BryanSmithDev/HeliosWatch/HeliosWatch_Documentation/Images/androidAppFilters.png

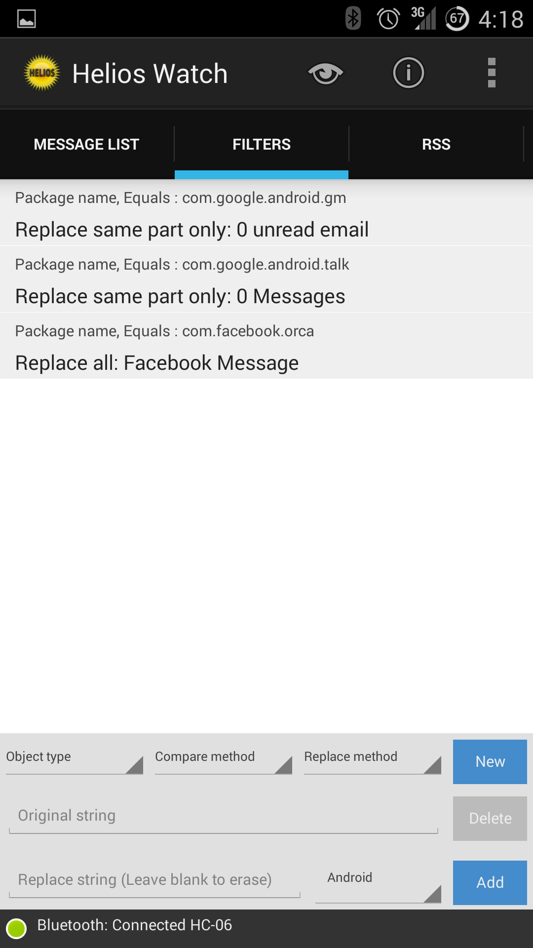
HeliosWatch_Documentation/Images/androidAppFilters.png
