BryanSmithDev/HeliosWatch/HeliosWatch_Documentation/Images/androidAppMessageList.png

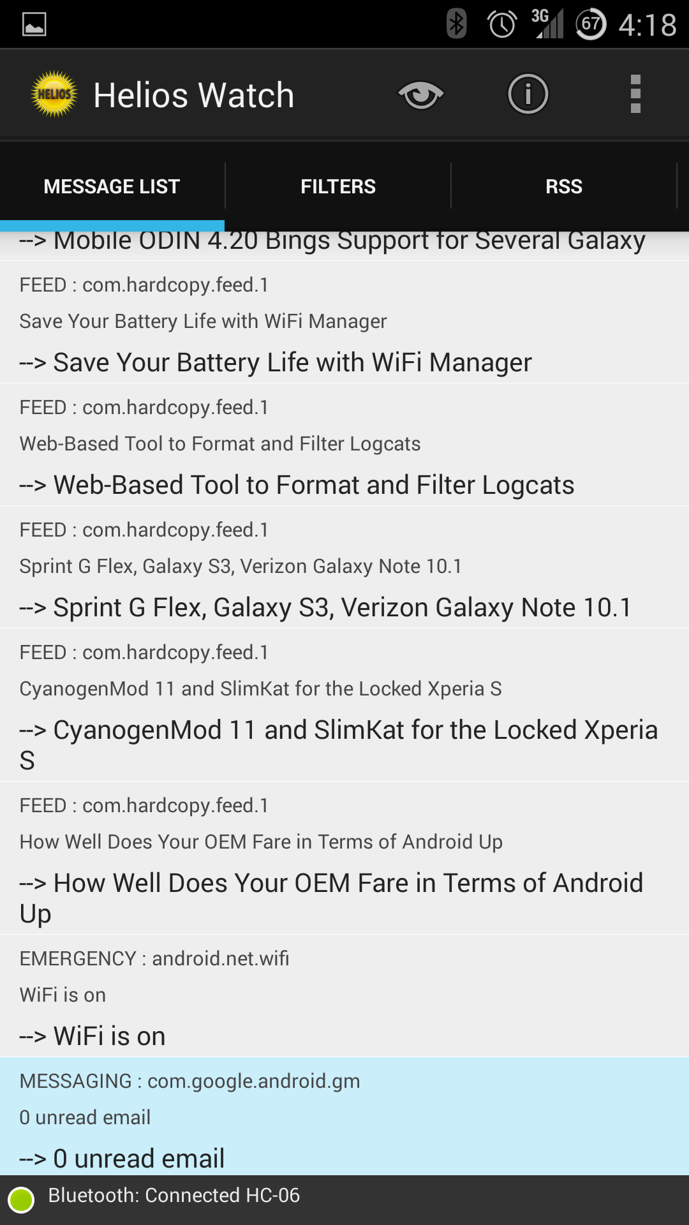
HeliosWatch_Documentation/Images/androidAppMessageList.png
