BryanSmithDev/HeliosWatch/HeliosWatch_Documentation/Images/androidAppRSS.png

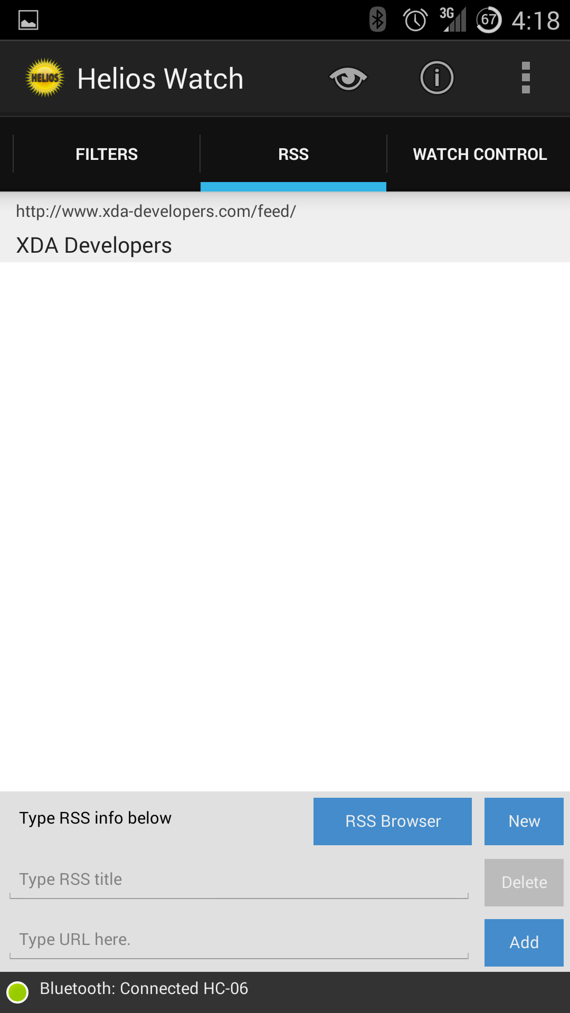
HeliosWatch_Documentation/Images/androidAppRSS.png
