BryanSmithDev/HeliosWatch/HeliosWatch_Documentation/Images/androidAppWatchControl.png

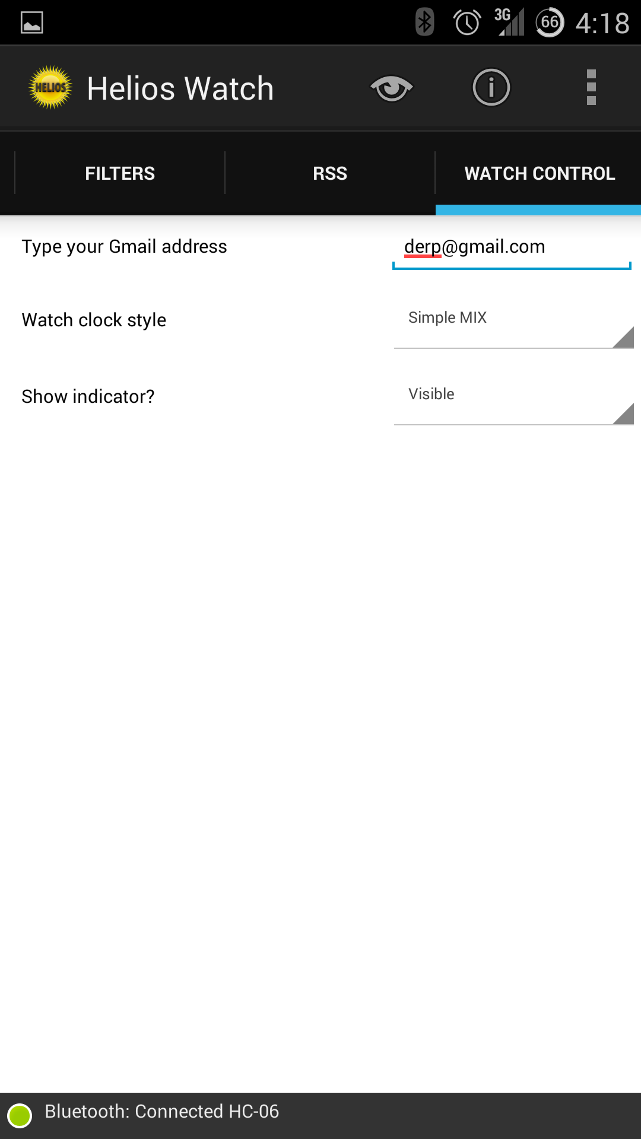
HeliosWatch_Documentation/Images/androidAppWatchControl.png
