BryanSmithDev/HeliosWatch/HeliosWatch_Documentation/Images/BatteryPrep1.jpg

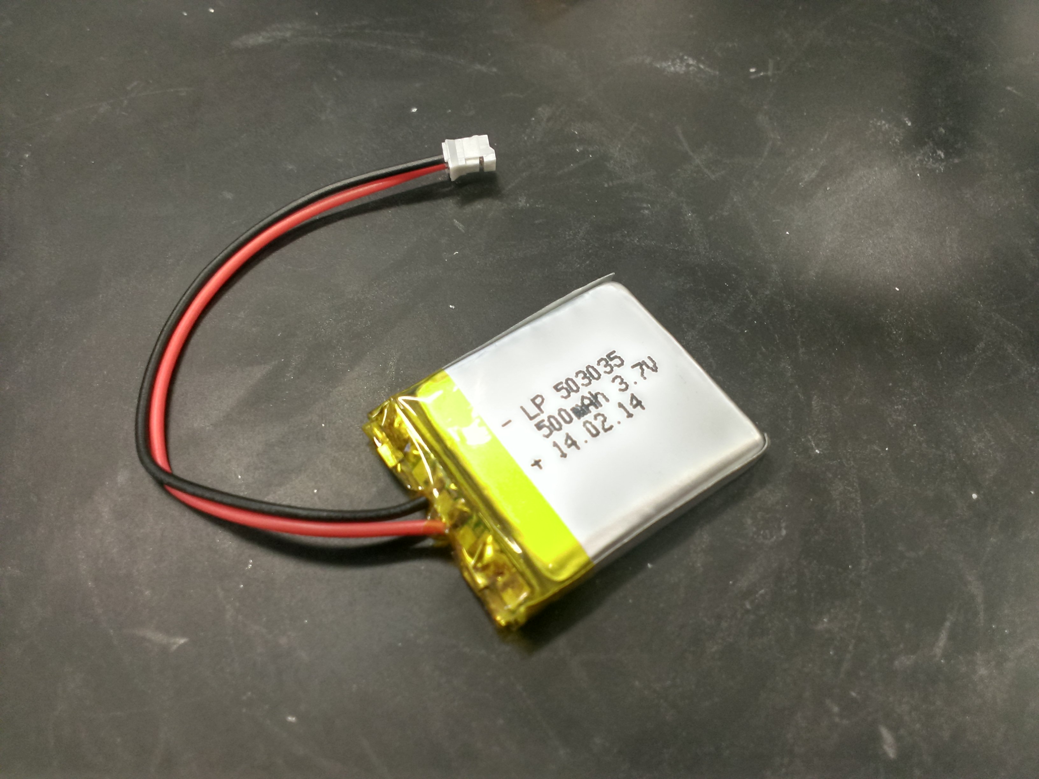
HeliosWatch_Documentation/Images/BatteryPrep1.jpg
