BryanSmithDev/HeliosWatch/HeliosWatch_Documentation/Images/BatteryPrep2.jpg

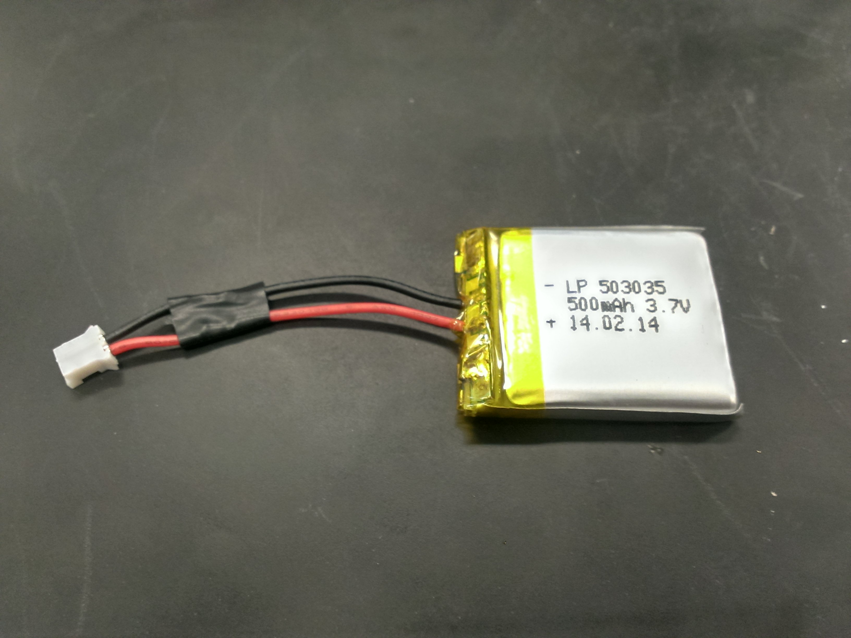
HeliosWatch_Documentation/Images/BatteryPrep2.jpg
