BryanSmithDev/HeliosWatch/HeliosWatch_Documentation/Images/coverDisplay.jpg

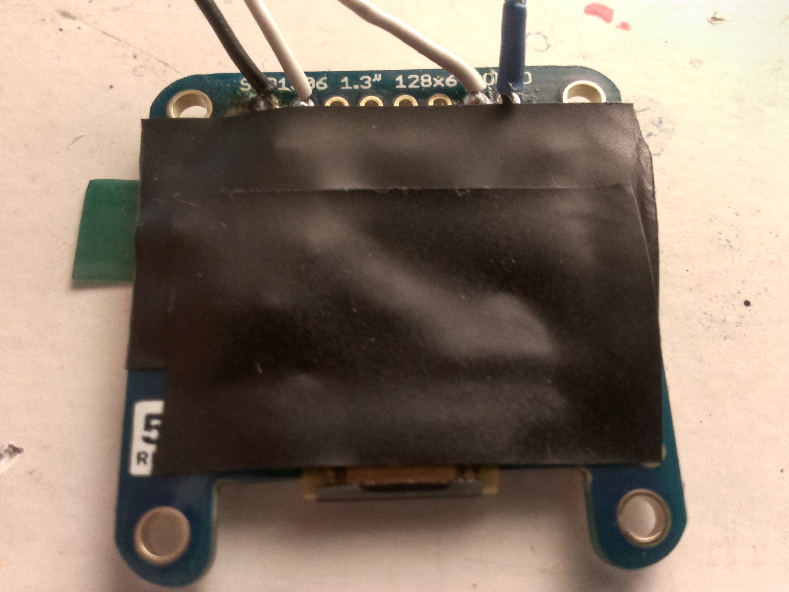
HeliosWatch_Documentation/Images/coverDisplay.jpg
