BryanSmithDev/HeliosWatch/HeliosWatch_Documentation/Images/DisplayPrep1.png

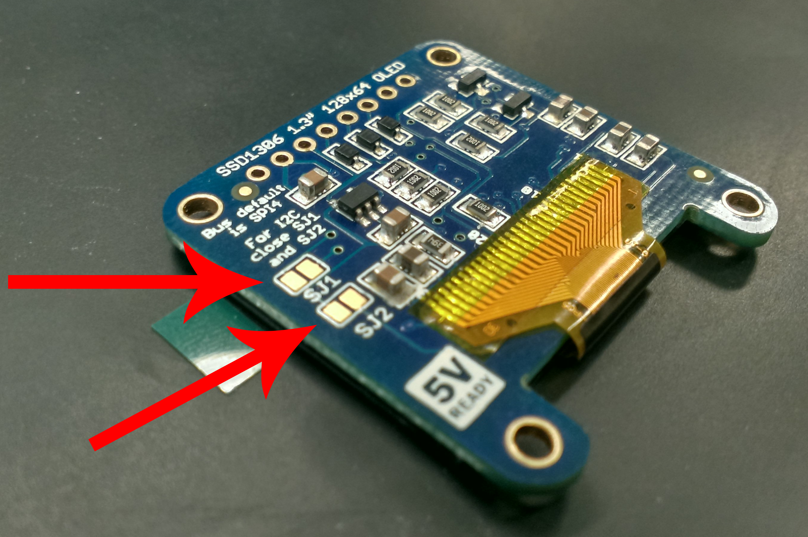
HeliosWatch_Documentation/Images/DisplayPrep1.png
