BryanSmithDev/HeliosWatch/HeliosWatch_Documentation/Images/finalBeforeCase.jpg

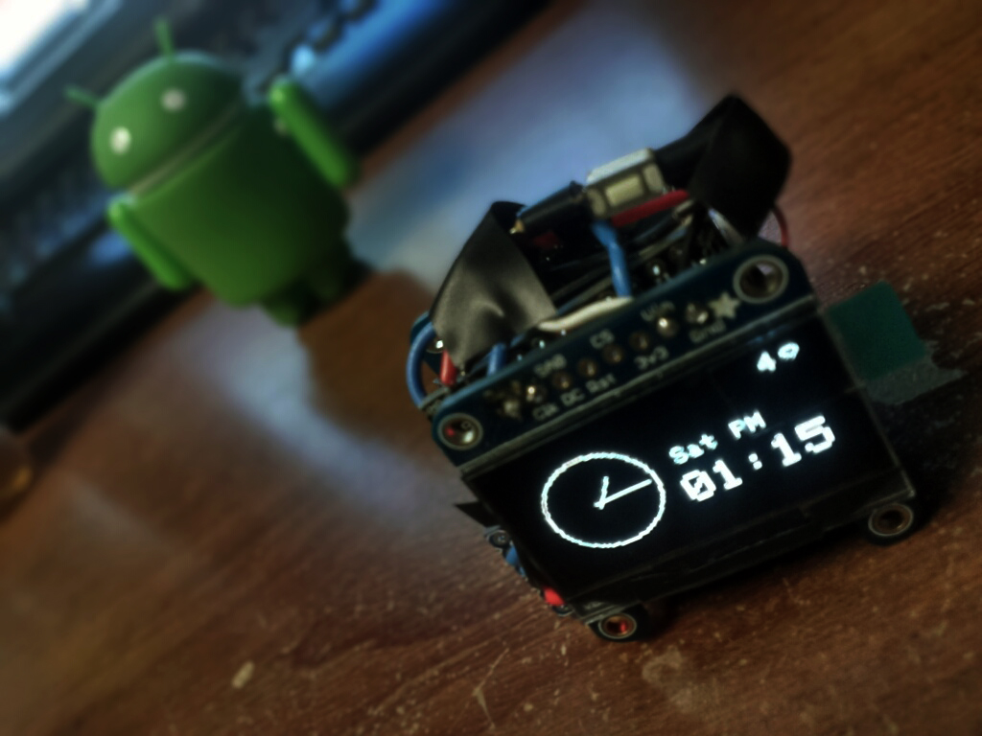
HeliosWatch_Documentation/Images/finalBeforeCase.jpg
