BryanSmithDev/HeliosWatch/HeliosWatch_Documentation/Images/FTDIPrep1.png

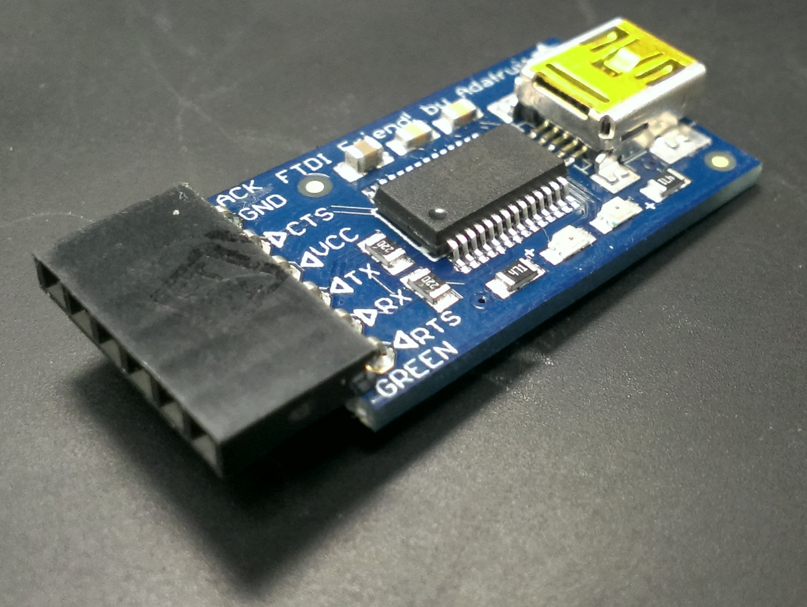
HeliosWatch_Documentation/Images/FTDIPrep1.png
