BryanSmithDev/HeliosWatch/HeliosWatch_Documentation/Images/heliosCase2.jpg

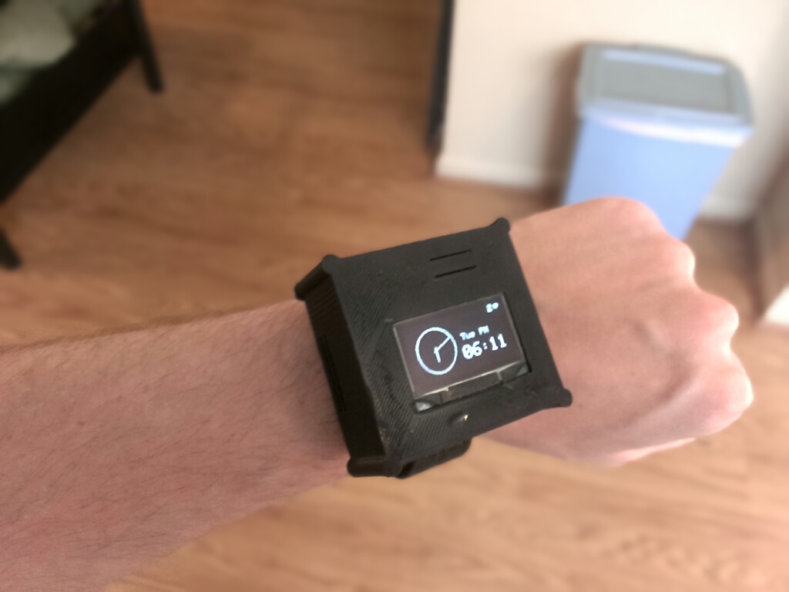
HeliosWatch_Documentation/Images/heliosCase2.jpg
