BryanSmithDev/HeliosWatch/HeliosWatch_Documentation/Images/heliosCase.jpg

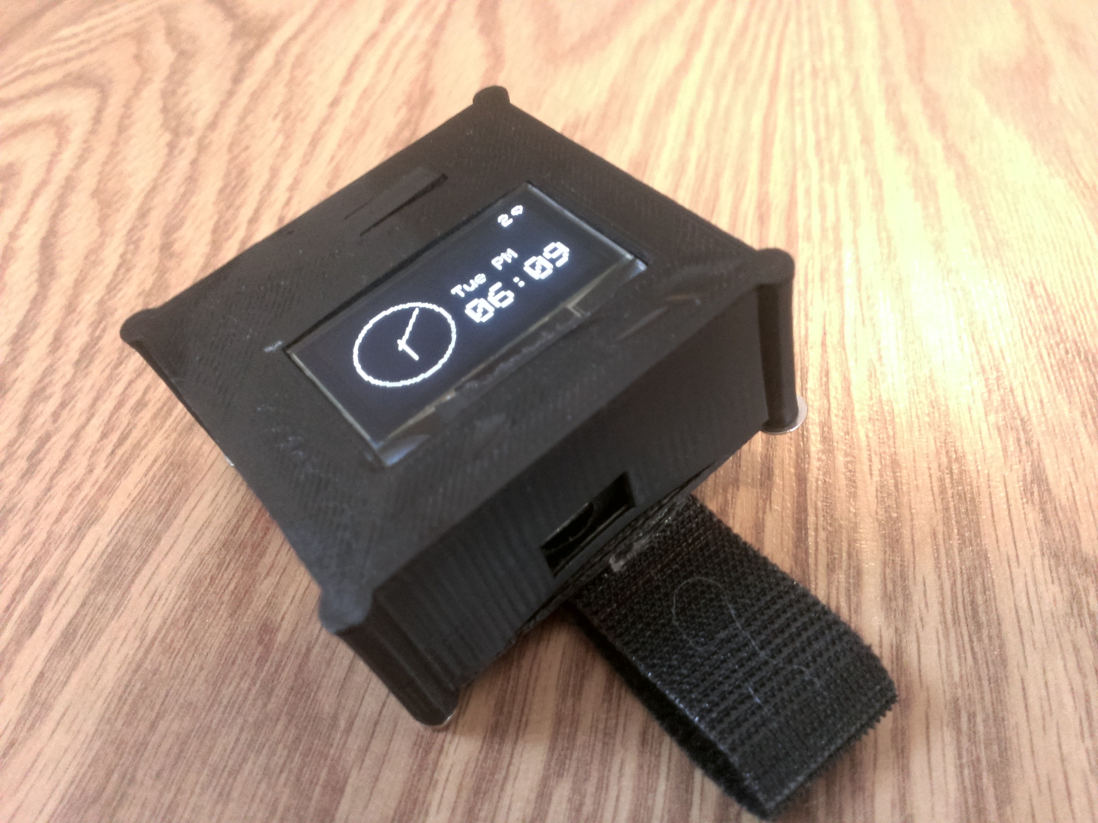
HeliosWatch_Documentation/Images/heliosCase.jpg
