BryanSmithDev/HeliosWatch/HeliosWatch_Documentation/Images/HeliosWatchDiagram.png

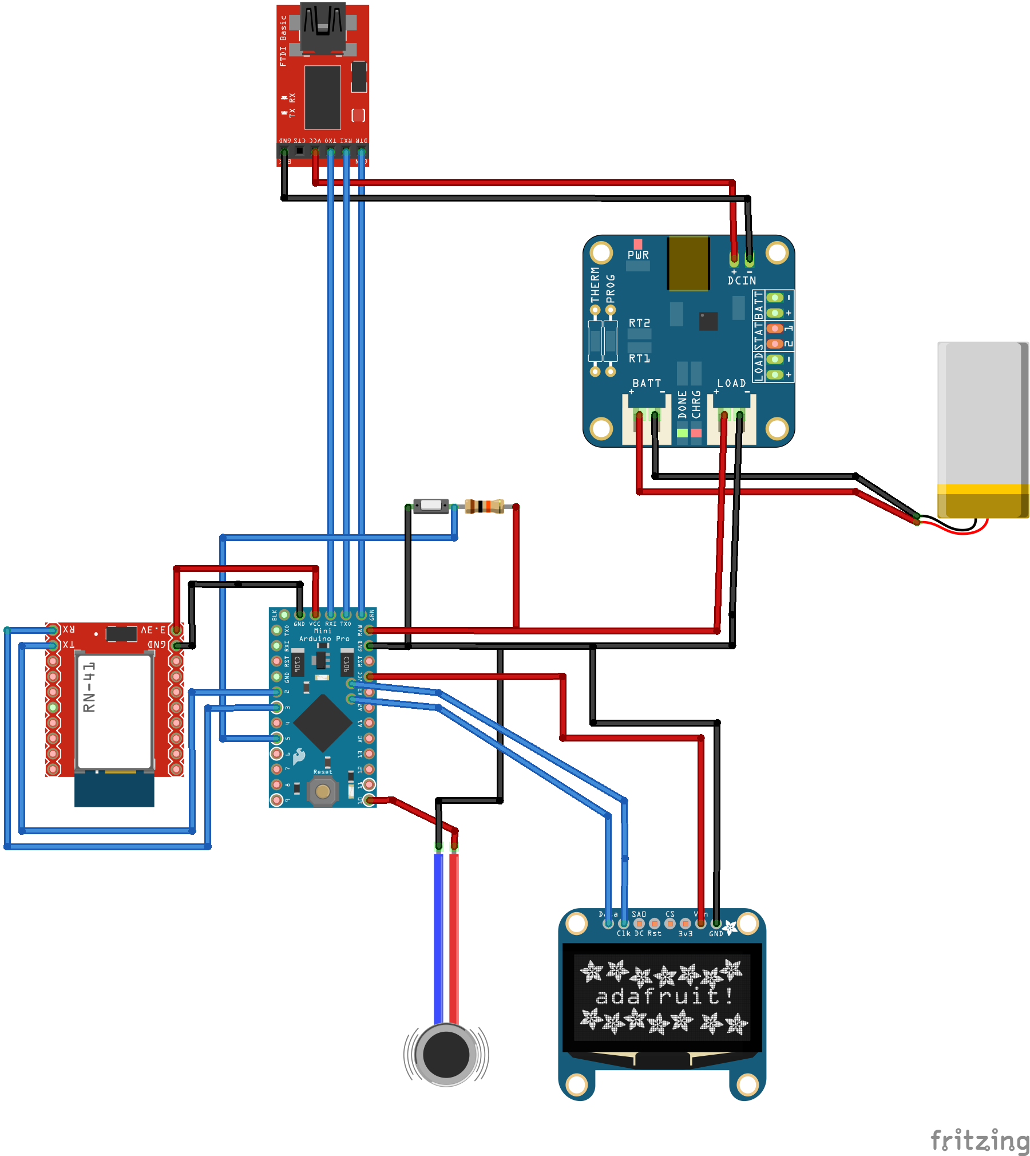
HeliosWatch_Documentation/Images/HeliosWatchDiagram.png
