BryanSmithDev/HeliosWatch/HeliosWatch_Documentation/Images/LayerLayoutsSide.png

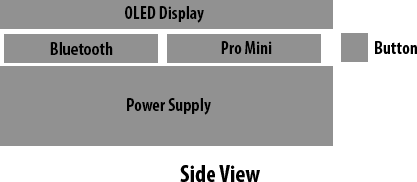
HeliosWatch_Documentation/Images/LayerLayoutsSide.png
