BryanSmithDev/HeliosWatch/HeliosWatch_Documentation/Images/LayerLayoutsTop.png

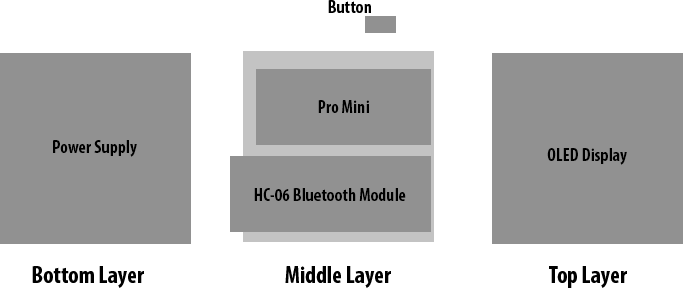
HeliosWatch_Documentation/Images/LayerLayoutsTop.png
