BryanSmithDev/HeliosWatch/HeliosWatch_Documentation/Images/PowerSupply1.jpg

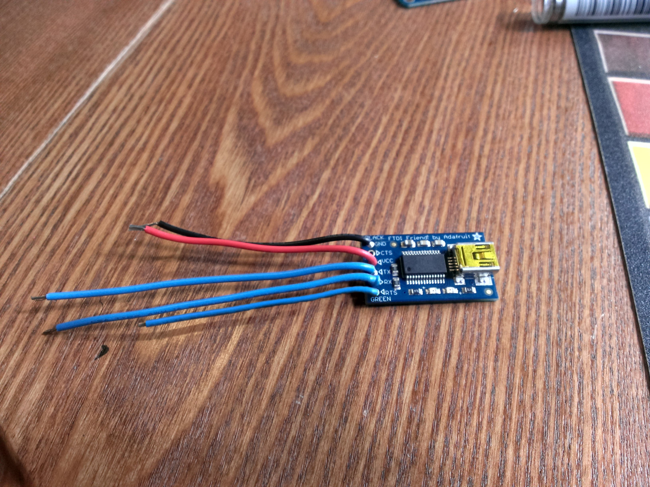
HeliosWatch_Documentation/Images/PowerSupply1.jpg
