BryanSmithDev/HeliosWatch/HeliosWatch_Documentation/Images/PowerSupply2.jpg

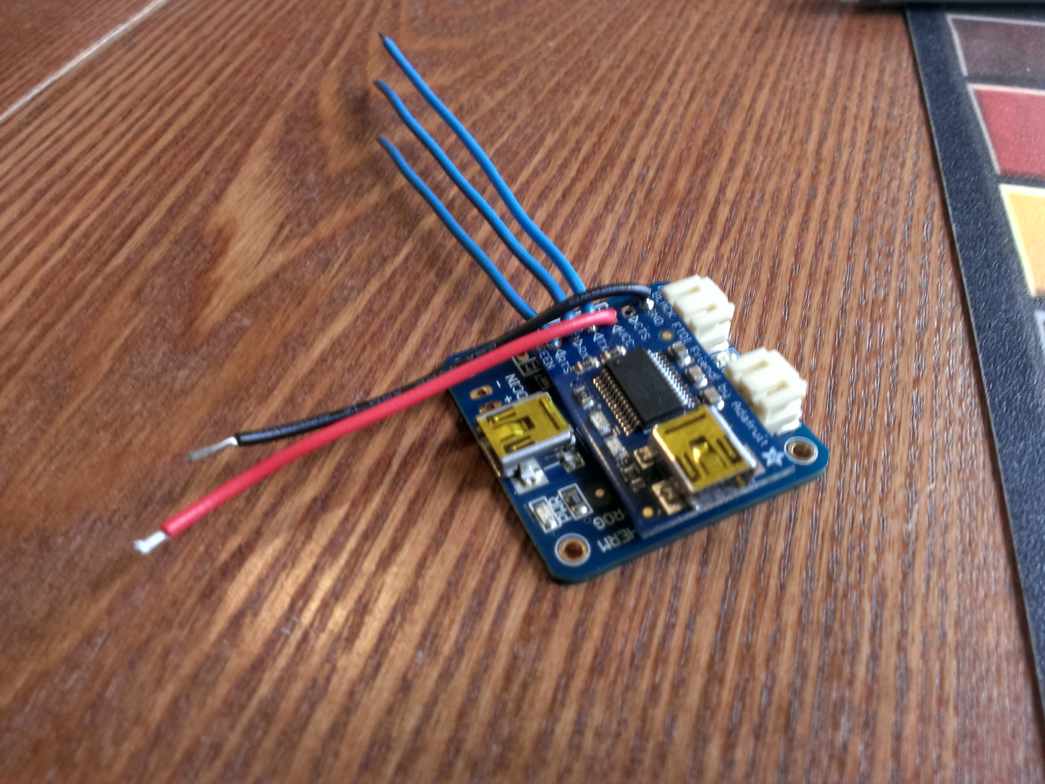
HeliosWatch_Documentation/Images/PowerSupply2.jpg
