BryanSmithDev/HeliosWatch/HeliosWatch_Documentation/Images/PowerSupply4.jpg

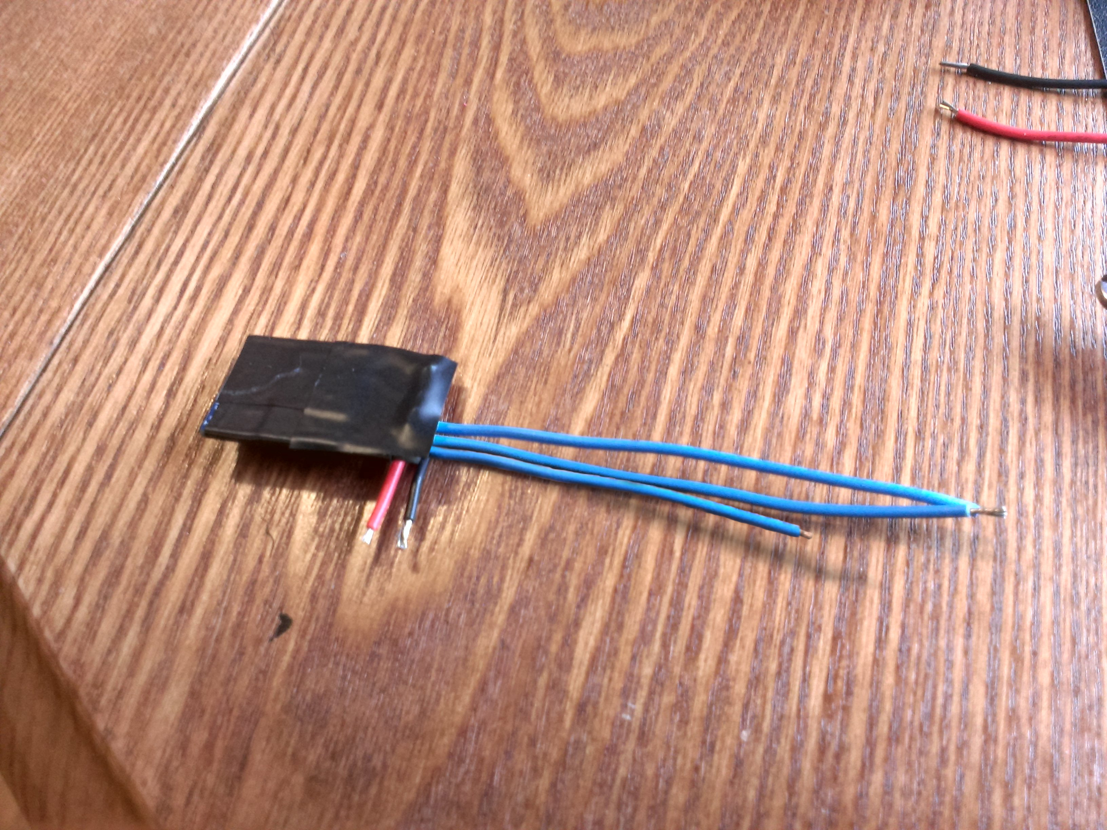
HeliosWatch_Documentation/Images/PowerSupply4.jpg
