BryanSmithDev/HeliosWatch/HeliosWatch_Documentation/Images/PowerSupply5.jpg

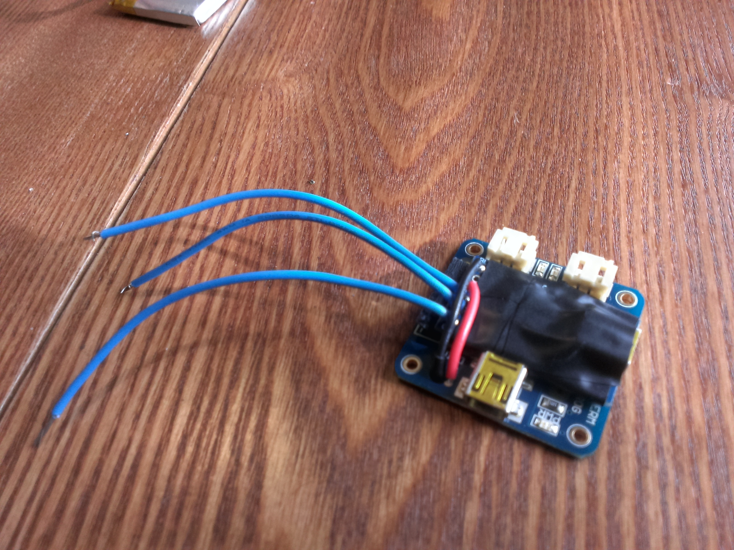
HeliosWatch_Documentation/Images/PowerSupply5.jpg
