BryanSmithDev/HeliosWatch/HeliosWatch_Documentation/Images/PowerSupply7.jpg

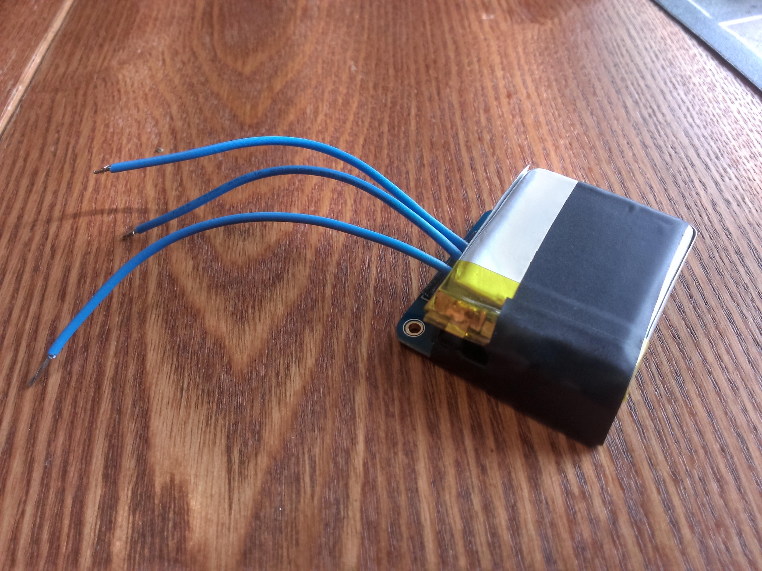
HeliosWatch_Documentation/Images/PowerSupply7.jpg
