BryanSmithDev/HeliosWatch/HeliosWatch_Documentation/Images/watchBottomSide.jpg

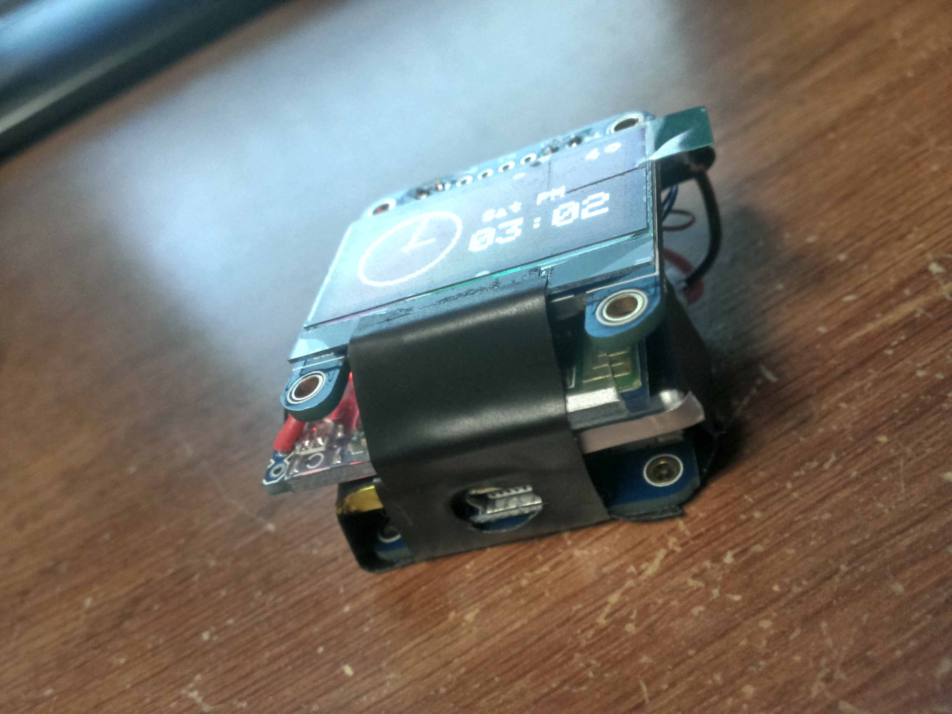
HeliosWatch_Documentation/Images/watchBottomSide.jpg
