BryanSmithDev/HeliosWatch/HeliosWatch_Documentation/Images/watchRightSide.jpg

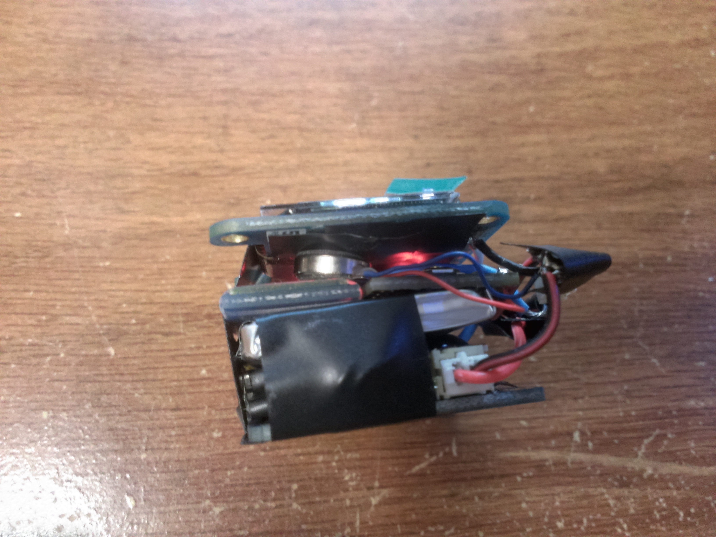
HeliosWatch_Documentation/Images/watchRightSide.jpg
