BryanSmithDev/HeliosWatch/HeliosWatch_Documentation/Images/watchTop.jpg

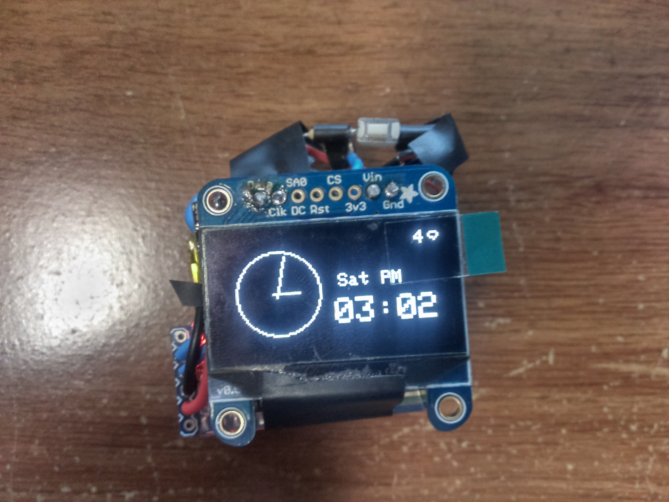
HeliosWatch_Documentation/Images/watchTop.jpg
