BryanSmithDev/HeliosWatch/HeliosWatch_Documentation/Images/watchTopSide.jpg

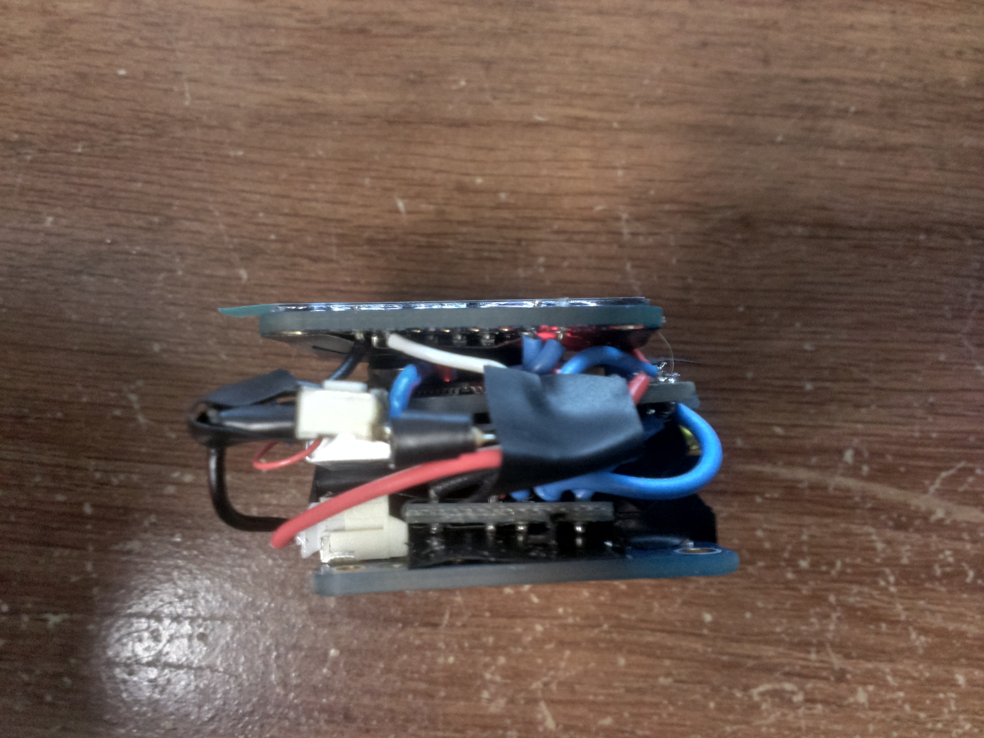
HeliosWatch_Documentation/Images/watchTopSide.jpg
