BryanSmithDev/HeliosWatch/HeliosWatch_Arduino/HeliosWatchArduino/bitmap.h

/*
 This project, dubbed Helios (God of Day/Night Cycle or God of the 
 Sun), is based off of Tortuga's RetroWatch to create a Bluetooth
 enabled smart watch using an Arduino that will pair with your Android
 device. Once paired, the smart watch can not only display the time 
 and date, but notifications from your Android device as well. 
 Additionally, the the watch can also display RSS feeds and system
 information, all of which can be filtered from the Android app designed
 for the watch. Modifications from Tortuga's RetroWatch include, 
 a larger screen, larger battery, vibration (haptic feedback),
 and internal battery charging while maintaining serial connection.

 Below is the RetroWatch Info
*/
/*
    RetroWatch Arduino is a part of open source smart watch project.
    Copyright (C) 2014  Suh Young Bae

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
    You should have received a copy of the GNU General Public License
    along with this program.  If not, see [http://www.gnu.org/licenses/].
*/
/*
Retro Watch Arduino v1.0

  Get the latest version, android host app, source code and guide doc at 
  ------> https://github.com/godstale/retrowatch
  ------> or http://www.hardcopyworld.com

Written by Suh Young Bae (godstale@hotmail.com)
All text above must be included in any redistribution
*/


////////////////////////////////////////////////////
// 16x24 Logo
////////////////////////////////////////////////////
const unsigned char PROGMEM IMG_logo_24x24[] = {
0x07,0xff,0xe0,
0x07,0xff,0xe0,
0x07,0xff,0xe0,
0x08,0x10,0x10,
0x10,0x10,0x08,
0x10,0x00,0x08,
0x10,0x00,0x08,
0x10,0x00,0x08,
0x10,0x00,0x08,
0x10,0x02,0x08,
0x10,0x04,0x08,
0x10,0x08,0x0c,
0x1c,0x10,0x3c,
0x10,0x08,0x0c,
0x10,0x08,0x08,
0x10,0x04,0x08,
0x10,0x04,0x08,
0x10,0x02,0x08,
0x10,0x02,0x08,
0x10,0x10,0x08,
0x08,0x10,0x10,
0x07,0xff,0xe0,
0x07,0xff,0xe0,
0x07,0xff,0xe0
}; 

////////////////////////////////////////////////////
// 8x8 Indicator
////////////////////////////////////////////////////
const unsigned char PROGMEM IMG_indicator_emg[] = {
0x00,
0x18,
0x18,
0x18,
0x00,
0x18,
0x00,
0x00
}; 

const unsigned char PROGMEM IMG_indicator_msg[] = {
0x00,
0x3c,
0x42,
0x42,
0x34,
0x08,
0x00,
0x00
}; 

////////////////////////////////////////////////////
// 16x16 icon bitmap matrix
////////////////////////////////////////////////////

#define GET_ICON(A) ICON_BITMAP_##A

//----- Change below count if you added new icon
#define ICON_ARRAY_SIZE 65

const unsigned char PROGMEM ICON_BITMAP_1[] = {
0x00,0x00,
0x00,0x00,
0x04,0x40,
0x07,0xc0,
0x0f,0xe0,
0x0b,0xa0,
0x1f,0xf0,
0x00,0x00,
0x5f,0xf4,
0x5f,0xf4,
0x5f,0xf4,
0x5f,0xf4,
0x1f,0xf0,
0x0c,0x60,
0x0c,0x60,
0x00,0x00
};
const unsigned char PROGMEM ICON_BITMAP_2[] = {
0x00,0x00,
0x00,0x00,
0x03,0x80,
0x06,0xc0,
0x03,0x80,
0x03,0x80,
0x03,0x80,
0x1f,0xf0,
0x03,0x80,
0x03,0x80,
0x43,0x84,
0x63,0x8c,
0x77,0xdc,
0x3f,0xf8,
0x1c,0x70,
0x00,0x00
}; 
const unsigned char PROGMEM ICON_BITMAP_3[] = {
0x00,0x00,
0x00,0x00,
0x00,0xc0,
0x01,0xc0,
0x01,0x80,
0x1d,0x70,
0x3f,0xf8,
0x7f,0xf0,
0x7f,0xe0,
0x7f,0xe0,
0x7f,0xe0,
0x7f,0xf0,
0x3f,0xf8,
0x1f,0xf0,
0x0e,0xe0,
0x00,0x00
}; 
const unsigned char PROGMEM ICON_BITMAP_4[] = {
0x00,0x00,
0x00,0x00,
0x00,0x00,
0x00,0x00,
0x5a,0xac,
0x5a,0xac,
0x5a,0xac,
0x5a,0xac,
0x5a,0xac,
0x5a,0xac,
0x02,0x08,
0x56,0xa8,
0x00,0x00,
0x00,0x00,
0x00,0x00,
0x00,0x00
}; 
const unsigned char PROGMEM ICON_BITMAP_5[] = {
0x00,0x00,
0x00,0x00,
0x00,0x00,
0x00,0x00,
0x00,0x00,
0x3f,0xfc,
0x20,0x04,
0x6d,0xb4,
0x6d,0xb4,
0x6d,0xb4,
0x20,0x04,
0x3f,0xfc,
0x00,0x00,
0x00,0x00,
0x00,0x00,
0x00,0x00
}; 
const unsigned char PROGMEM ICON_BITMAP_6[] = {
0x00,0x00,
0x00,0x00,
0x00,0x00,
0x00,0x00,
0x00,0x00,
0x3f,0xfc,
0x20,0x04,
0x61,0xb4,
0x61,0xb4,
0x61,0xb4,
0x20,0x04,
0x3f,0xfc,
0x00,0x00,
0x00,0x00,
0x00,0x00,
0x00,0x00
}; 
const unsigned char PROGMEM ICON_BITMAP_7[] = {
0x00,0x00,
0x00,0x00,
0x00,0x00,
0x00,0x00,
0x00,0x00,
0x3f,0xfc,
0x20,0x04,
0x60,0x34,
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
0x40,0x02,
0x3f,0xfc,
0x00,0x00,
0x00,0x00,
0x00,0x00,
0x00,0x00
};

const unsigned char PROGMEM ICON_BITMAP_65[] = {
0x00,0x00,
0x00,0x00,
0x3f,0xe0,
0x10,0x40,
0x08,0x80,
0x05,0x00,
0x02,0x00,
0x02,0x00,
0x02,0x00,
0x00,0x0c,
0x00,0x6c,
0x03,0x6c,
0x1b,0x6c,
0x1b,0x6c,
0x00,0x00,
0x00,0x00
};

//----- Add new icon to below array
//----- You can access icon by index
PROGMEM const unsigned char* bitmap_array[] = {
ICON_BITMAP_1, ICON_BITMAP_2, ICON_BITMAP_3, ICON_BITMAP_4, ICON_BITMAP_5,     
ICON_BITMAP_6, ICON_BITMAP_7, ICON_BITMAP_8, ICON_BITMAP_9, ICON_BITMAP_10,  // ~10

ICON_BITMAP_11, ICON_BITMAP_12, ICON_BITMAP_13, ICON_BITMAP_14, ICON_BITMAP_15,     
ICON_BITMAP_16, ICON_BITMAP_17, ICON_BITMAP_18, ICON_BITMAP_19, ICON_BITMAP_20,  // ~20

ICON_BITMAP_21, ICON_BITMAP_22, ICON_BITMAP_23, ICON_BITMAP_24, ICON_BITMAP_25,     
ICON_BITMAP_26, ICON_BITMAP_27, ICON_BITMAP_28, ICON_BITMAP_29, ICON_BITMAP_30,  // ~30

ICON_BITMAP_31, ICON_BITMAP_32, ICON_BITMAP_33, ICON_BITMAP_34, ICON_BITMAP_35,     
ICON_BITMAP_36, ICON_BITMAP_37, ICON_BITMAP_38, ICON_BITMAP_39, ICON_BITMAP_40,  // ~40

ICON_BITMAP_41, ICON_BITMAP_42, ICON_BITMAP_43, ICON_BITMAP_44, ICON_BITMAP_45,     
ICON_BITMAP_46, ICON_BITMAP_47, ICON_BITMAP_48, ICON_BITMAP_49, ICON_BITMAP_50,  // ~50

ICON_BITMAP_51, ICON_BITMAP_52, ICON_BITMAP_53, ICON_BITMAP_54, ICON_BITMAP_55,     
ICON_BITMAP_56, ICON_BITMAP_57, ICON_BITMAP_58, ICON_BITMAP_59, ICON_BITMAP_60,  // ~60

ICON_BITMAP_61, ICON_BITMAP_62, ICON_BITMAP_63, ICON_BITMAP_64, ICON_BITMAP_65  // ~65
};

/*
 * Check icon name. It's arranged by the sequence of icon array.
 
ICON_BITMAP_android, ICON_BITMAP_ankor, ICON_BITMAP_apple, ICON_BITMAP_barcode, ICON_BITMAP_batt_1_full,     
ICON_BITMAP_batt_2_med, ICON_BITMAP_batt_3_low, ICON_BITMAP_batt_4_empty, ICON_BITMAP_bookmark, ICON_BITMAP_calendar,  // 0~9

ICON_BITMAP_call, ICON_BITMAP_camera, ICON_BITMAP_cancel, ICON_BITMAP_character_skull, ICON_BITMAP_character1,     
ICON_BITMAP_character2, ICON_BITMAP_character3, ICON_BITMAP_character4, ICON_BITMAP_chart, ICON_BITMAP_chat,  // 10~19

ICON_BITMAP_chrome, ICON_BITMAP_clip, ICON_BITMAP_clock, ICON_BITMAP_copy, ICON_BITMAP_denied,     
ICON_BITMAP_document, ICON_BITMAP_download, ICON_BITMAP_earth, ICON_BITMAP_email, ICON_BITMAP_folder,  // 20~29

ICON_BITMAP_home, ICON_BITMAP_kittcharacter_y, ICON_BITMAP_list, ICON_BITMAP_movie, ICON_BITMAP_music,     
ICON_BITMAP_navigator, ICON_BITMAP_pen, ICON_BITMAP_person, ICON_BITMAP_picture, ICON_BITMAP_pill,  // 30~39

ICON_BITMAP_power, ICON_BITMAP_power_plug, ICON_BITMAP_power_unplug, ICON_BITMAP_print, ICON_BITMAP_rain,     
ICON_BITMAP_refresh, ICON_BITMAP_rss, ICON_BITMAP_save, ICON_BITMAP_security_lock, ICON_BITMAP_security_unlock,  // 40~49

ICON_BITMAP_settings, ICON_BITMAP_smile, ICON_BITMAP_social_facebook, ICON_BITMAP_twitter, ICON_BITMAP_tag,     
ICON_BITMAP_trade, ICON_BITMAP_trash, ICON_BITMAP_unknown, ICON_BITMAP_usim, ICON_BITMAP_wait,  // 50~59

ICON_BITMAP_warning, ICON_BITMAP_wifi, ICON_BITMAP_windows, ICON_BITMAP_z_cloud, ICON_BITMAP_z_rfstatus,    // 60~64

*/
